Myriadbits/Myriadclock/src/DisplayStateToilet.h

#pragma once

#include "DisplayStateBase.h"

///////////////////////////////////////////////////////////////////////////////
// Base class for all display states
// Command line interpreter
///////////////////////////////////////////////////////////////////////////////
class DisplayStateToilet : public DisplayStateBase
{
public:
    DisplayStateToilet() : DisplayStateBase("toilet") 
    {
    }

    virtual void Initialize(CRGB* pLEDs, BLEConfig* pConfig, DisplayStateManager *pManager);
    virtual bool HandleLoop(unsigned long epochTime, time_t localTime);  

private:
    static uint8_t     s_toiletSign[16 * 16];
    uint8_t     m_nWordIndexTop;
    uint8_t     m_nWordIndexBottom;
};
