Myriadbits/Myriadclock/src/ClockLayoutEN_V2.h

///////////////////////////////////////////////////////////////////////////////
//
// Definition of the myriadclock display layout for the English plate
//
// COPYRIGHT NOTICE                                                           
// ================
// Copyright (c) 2026, Jochem Bakker <Jochem@myriadbits.com>
//
// Published under the Internet Systems Consortium (ISC) license:
// Permission to use, copy, modify, and/or distribute this software for any
// purpose with or without fee is hereby granted, provided that the above
// copyright notice and this permission notice appear in all copies.
//
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
#pragma once

#include "ClockLayoutBase.h"

// How many leds are connected?
#define NUM_LEDS    256
#define NUM_ROWS    16
#define NUM_COLS    16

//
// Latest characters:
//   0123456789012345
// ----------------
// 0|TWENTY-FIVE•TOL•
// 1|TENHALFNPASTOBO•
// 2|QUARTEROPASTORL•
// 3|•BIRTHDAYGOODBT•
// 4|THREEIGHTMORNING
// 5|TWONESEVENOWIFIW
// 6|FOURTWELVEBREAKO
// 7|TENINELEVENFASTR
// 8|FIVESIX•O'CLOCKD
// 9|LUNCHDINNERTIMEC
// 0|MOTUWETHFRSASUNL
// 1|101121314151617O
// 2|181922023242526X
// 3|27282930@JANFEBE
// 4|MARAPRMAYJUNJULL
// 5|AUGSEPOCTNOVDEC•
//


// Word definitions, {-1,-1} or WEND terminated (led numbers start at 0)

static const ledpos_t ENV2_minute_1  [] = { {15,0}, WEND};
static const ledpos_t ENV2_minute_2  [] = { {15,0}, {15,1}, WEND};
static const ledpos_t ENV2_minute_3  [] = { {15,0}, {15,1}, {15,2}, WEND};
static const ledpos_t ENV2_minute_4  [] = { {15,0}, {15,1}, {15,2}, {15,3}, WEND};
static const ledpos_t ENV2_minute_5  [] = { {7,0}, {8,0}, {9,0}, {10,0}, WEND};
static const ledpos_t ENV2_minute_10 [] = { {0,1}, {1,1}, {2,1}, WEND};
static const ledpos_t ENV2_quarter   [] = { {0,2}, {1,2}, {2,2}, {3,2}, {4,2}, {5,2}, {6,2}, WEND};
static const ledpos_t ENV2_minute_20 [] = { {0,0}, {1,0}, {2,0}, {3,0}, {4,0}, {5,0}, WEND};
static const ledpos_t ENV2_minute_25 [] = { {0,0}, {1,0}, {2,0}, {3,0}, {4,0}, {5,0}, {6,0}, {7,0}, {8,0}, {9,0}, {10,0}, WEND};

static const ledpos_t ENV2_pulse     [] = { {15,15}, WEND};

static const ledpos_t ENV2_past1     [] = { {8,1}, {9,1}, {10,1}, {11,1}, WEND};
static const ledpos_t ENV2_past2     [] = { {8,2}, {9,2}, {10,2}, {11,2}, WEND};
static const ledpos_t ENV2_to0       [] = { {12,0}, {13,0}, WEND}; // Line 0
static const ledpos_t ENV2_to1       [] = { {11,1}, {12,1}, WEND}; // Line 1
static const ledpos_t ENV2_to2       [] = { {11,2}, {12,2}, WEND}; // Line 2

static const ledpos_t ENV2_half      [] = { {3,1}, {4,1}, {5,1}, {6,1}, {8,1}, {9,1}, {10,1}, {11,1}, WEND}; // It is always "half past"

static const ledpos_t ENV2_hour_1    [] = { {2,5}, {3,5}, {4,5}, WEND};
static const ledpos_t ENV2_hour_2    [] = { {0,5}, {1,5}, {2,5}, WEND};
static const ledpos_t ENV2_hour_3    [] = { {0,4}, {1,4}, {2,4}, {3,4}, {4,4}, WEND};
static const ledpos_t ENV2_hour_4    [] = { {0,6}, {1,6}, {2,6}, {3,6}, WEND};
static const ledpos_t ENV2_hour_5    [] = { {0,8}, {1,8}, {2,8}, {3,8}, WEND};
static const ledpos_t ENV2_hour_6    [] = { {4,8}, {5,8}, {6,8}, WEND};
static const ledpos_t ENV2_hour_7    [] = { {5,5}, {6,5}, {7,5}, {8,5}, {9,5}, WEND};
static const ledpos_t ENV2_hour_8    [] = { {4,4}, {5,4}, {6,4}, {7,4}, {8,4}, WEND};
static const ledpos_t ENV2_hour_9    [] = { {2,7}, {3,7}, {4,7}, {5,7}, WEND};
static const ledpos_t ENV2_hour_10   [] = { {0,7}, {1,7}, {2,7}, WEND};
static const ledpos_t ENV2_hour_11   [] = { {5,7}, {6,7}, {7,7}, {8,7}, {9,7}, {10,7}, WEND};
static const ledpos_t ENV2_hour_12   [] = { {4,6}, {5,6}, {6,6}, {7,6}, {8,6}, {9,6}, WEND};
static const ledpos_t ENV2_hour_full [] = { {8,8}, {9,8}, {10,8}, {11,8}, {12,8}, {13,8}, {14,8}, WEND};


static const ledpos_t ENV2_monday    [] = { {0,10}, {1,10}, WEND};
static const ledpos_t ENV2_tuesday   [] = { {2,10}, {3,10}, WEND};
static const ledpos_t ENV2_wednesday [] = { {4,10}, {5,10}, WEND};
static const ledpos_t ENV2_thursday  [] = { {6,10}, {7,10}, WEND};
static const ledpos_t ENV2_friday    [] = { {8,10}, {9,10}, WEND};
static const ledpos_t ENV2_saturday  [] = { {10,10}, {11,10}, WEND};
static const ledpos_t ENV2_sunday    [] = { {12,10}, {13,10}, {14,10}, WEND};

static const ledpos_t ENV2_day0      [] = { {1,11}, WEND};
static const ledpos_t ENV2_day1      [] = { {2,11}, WEND};
static const ledpos_t ENV2_day2      [] = { {4,11}, WEND};
static const ledpos_t ENV2_day3      [] = { {6,11}, WEND};
static const ledpos_t ENV2_day4      [] = { {8,11}, WEND};
static const ledpos_t ENV2_day5      [] = { {10,11}, WEND};
static const ledpos_t ENV2_day6      [] = { {12,11}, WEND};
static const ledpos_t ENV2_day7      [] = { {14,11}, WEND};
static const ledpos_t ENV2_day8      [] = { {1,12}, WEND};
static const ledpos_t ENV2_day9      [] = { {3,12}, WEND};
static const ledpos_t ENV2_day10     [] = { {0,11}, {1,11}, WEND};
static const ledpos_t ENV2_day11     [] = { {2,11}, {3,11}, WEND};
static const ledpos_t ENV2_day12     [] = { {3,11}, {4,11}, WEND};
static const ledpos_t ENV2_day13     [] = { {5,11}, {6,11}, WEND};
static const ledpos_t ENV2_day14     [] = { {7,11}, {8,11}, WEND};
static const ledpos_t ENV2_day15     [] = { {9,11}, {10,11}, WEND};
static const ledpos_t ENV2_day16     [] = { {11,11}, {12,11}, WEND};
static const ledpos_t ENV2_day17     [] = { {13,11}, {14,11}, WEND};
static const ledpos_t ENV2_day18     [] = { {0,12}, {1,12}, WEND};
static const ledpos_t ENV2_day19     [] = { {2,12}, {3,12}, WEND};
static const ledpos_t ENV2_day20     [] = { {5,12}, {6,12}, WEND};
static const ledpos_t ENV2_day21     [] = { {4,11}, {5,11}, WEND};
static const ledpos_t ENV2_day22     [] = { {4,12}, {5,12}, WEND};
static const ledpos_t ENV2_day23     [] = { {7,12}, {8,12}, WEND};
static const ledpos_t ENV2_day24     [] = { {9,12}, {10,12}, WEND};
static const ledpos_t ENV2_day25     [] = { {11,12}, {12,12}, WEND};
static const ledpos_t ENV2_day26     [] = { {13,12}, {14,12}, WEND};
static const ledpos_t ENV2_day27     [] = { {0,13}, {1,13}, WEND};
static const ledpos_t ENV2_day28     [] = { {2,13}, {3,13}, WEND};
static const ledpos_t ENV2_day29     [] = { {4,13}, {5,13}, WEND};
static const ledpos_t ENV2_day30     [] = { {6,13}, {7,13}, WEND};
static const ledpos_t ENV2_day31     [] = { {6,11}, {7,11}, WEND};

static const ledpos_t ENV2_januari  [] = { {9,13}, {10,13}, {11,13}, WEND};
static const ledpos_t ENV2_februari [] = { {12,13}, {13,13}, {14,13}, WEND};
static const ledpos_t ENV2_march    [] = { {0,14}, {1,14}, {2,14}, WEND};
static const ledpos_t ENV2_april    [] = { {3,14}, {4,14}, {5,14}, WEND};
static const ledpos_t ENV2_may      [] = { {6,14}, {7,14}, {8,14}, WEND};
static const ledpos_t ENV2_june     [] = { {9,14}, {10,14}, {11,14}, WEND};
static const ledpos_t ENV2_july     [] = { {12,14}, {13,14}, {14,14}, WEND};
static const ledpos_t ENV2_august   [] = { {0,15}, {1,15}, {2,15}, WEND};
static const ledpos_t ENV2_september[] = { {3,15}, {4,15}, {5,15}, WEND};
static const ledpos_t ENV2_october  [] = { {6,15}, {7,15}, {8,15}, WEND};
static const ledpos_t ENV2_november [] = { {9,15}, {10,15}, {11,15}, WEND};
static const ledpos_t ENV2_december [] = { {12,15}, {13,15}, {14,15}, WEND};

static const ledpos_t ENV2_cloxel  [] = { {15,9}, {15,10}, {15,11}, {15,12}, {15,13}, {15,14}, WEND};
static const ledpos_t ENV2_word  [] = { {15,5}, {15,6}, {15,7}, {15,8}, WEND};
static const ledpos_t ENV2_bt [] = { {13,3}, {14,3}, WEND};
static const ledpos_t ENV2_passcode [] = { WEND};
static const ledpos_t ENV2_no  [] = { {9,5}, {10,5}, WEND};
static const ledpos_t ENV2_yes  [] = { {9,3}, {10,3}, {11,3}, {12,3}, WEND}; // Actually = GOOD
static const ledpos_t ENV2_wifi  [] = { {11,5}, {12,5}, {13,5}, {14,5}, WEND};

static const ledpos_t ENV2_birthday [] = { {1,3}, {2,3}, {3,3}, {4,3}, {5,3}, {6,3}, {7,3}, {8,3}, WEND};
static const ledpos_t ENV2_holiday [] = { WEND};
static const ledpos_t ENV2_party [] = { {6,3}, {7,3}, {8,3}, WEND}; // Actually not available, will display 'day'
static const ledpos_t ENV2_wakeup [] = { WEND};
static const ledpos_t ENV2_goodmorning [] = { {9,3}, {10,3}, {11,3}, {12,3}, {9,4}, {10,4}, {11,4}, {12,4}, {13,4}, {14,4}, {15,4}, WEND};

static const ledpos_t ENV2_breakfast [] = { {10,6}, {11,6}, {12,6}, {13,6}, {14,6}, {11,7}, {12,7}, {13,7}, {14,7}, WEND};
static const ledpos_t ENV2_lunch [] = { {0,9}, {1,9}, {2,9}, {3,9}, {4,9}, {11,9}, {12,9}, {13,9}, {14,9}, WEND};
static const ledpos_t ENV2_dinner [] = { {5,9}, {6,9}, {7,9}, {8,9}, {9,9}, {10,9}, {11,9}, {12,9}, {13,9}, {14,9}, WEND};

//
// EN clock layout V1
//
static const ledclocklayout_t s_layoutEN_V2 = 
{
    16,
    16,
    256,
    O_NORMAL,
    false,

    // Time display method
    TF_EN_5MIN,

    // Time parts
    {
        ENV2_pulse, EMPTY, ENV2_minute_1, ENV2_minute_2, ENV2_minute_3, ENV2_minute_4, ENV2_minute_5, EMPTY, EMPTY, EMPTY, EMPTY, ENV2_minute_10,
        EMPTY, EMPTY, EMPTY, EMPTY, ENV2_quarter, ENV2_minute_20, ENV2_minute_25, 
        ENV2_past2, ENV2_to0, ENV2_past1, ENV2_to1, ENV2_past2, ENV2_to2, ENV2_past1, ENV2_to0, ENV2_past2, ENV2_to0, 
        ENV2_half, ENV2_half, ENV2_hour_full
    },

    // 12x Hours
    {
        ENV2_hour_12, ENV2_hour_1, ENV2_hour_2, ENV2_hour_3, ENV2_hour_4, ENV2_hour_5, ENV2_hour_6, ENV2_hour_7, ENV2_hour_8, ENV2_hour_9, ENV2_hour_10, ENV2_hour_11         
    },

    // 7x Day of the week
    {
        ENV2_sunday, ENV2_monday, ENV2_tuesday, ENV2_wednesday, ENV2_thursday, ENV2_friday, ENV2_saturday
    },

    // 31x Day number
    {
        ENV2_day1, ENV2_day2, ENV2_day3, ENV2_day4, ENV2_day5, ENV2_day6, ENV2_day7, ENV2_day8, ENV2_day9, ENV2_day10, 
        ENV2_day11, ENV2_day12, ENV2_day13, ENV2_day14, ENV2_day15, ENV2_day16, ENV2_day17, ENV2_day18, ENV2_day19, ENV2_day20, 
        ENV2_day21, ENV2_day22, ENV2_day23, ENV2_day24, ENV2_day25, ENV2_day26, ENV2_day27, ENV2_day28, ENV2_day29, ENV2_day30, 
        ENV2_day31
    },

    // 12x Month
    {
        ENV2_januari, ENV2_februari, ENV2_march, ENV2_april, ENV2_may, ENV2_june, ENV2_july, ENV2_august, ENV2_september, ENV2_october, ENV2_november, ENV2_december
    },

    // Extra parts
    {
        ENV2_no,
        ENV2_yes,
        ENV2_wifi,
        ENV2_cloxel,
        ENV2_word,
        EMPTY,
        ENV2_bt,
        ENV2_passcode,
        ENV2_goodmorning,
        ENV2_birthday,
        ENV2_holiday,
        ENV2_party,
        ENV2_wakeup,
        ENV2_breakfast,
        ENV2_lunch,
        ENV2_dinner,
    },

    // 10x number
    {
        ENV2_day0, ENV2_day1, ENV2_day2, ENV2_day3, ENV2_day4, ENV2_day5, ENV2_day6, ENV2_day7, ENV2_day8, ENV2_day9
    }
};
