Myriadbits/Myriadclock/src/Myriadbitsfont5x6_3.h

#include "FontsBase.h"

const uint8_t JochemFont56Bitmaps[] PROGMEM = {
	0x55, 0x00, 0xB4, 0x00, 0x00, 0x00, 0x5F, 0x00, 
	0x06, 0xF8, 0x00, 0x00, 0x92, 0x00, 0x0A, 0xA0, 
	0x00, 0xC0, 0x6A, 0x00, 0x95, 0x00, 0x02, 0xA0, 
	0x00, 0x05, 0x00, 0x00, 0x12, 0x00, 0xF6, 0xDE, 
	0x00, 0xF8, 0xE7, 0xCE, 0x00, 0xE7, 0x9E, 0x00, 
	0xB7, 0x92, 0x00, 0xF3, 0x9E, 0x00, 0xF3, 0xDE, 
	0x00, 0xE4, 0x92, 0x00, 0xF7, 0xDE, 0x00, 0xF7, 
	0x9E, 0x00, 0x50, 0x58, 0x2A, 0x22, 0x00, 0x03, 
	0x80, 0x00, 0x88, 0xA8, 0x00, 0xE5, 0x04, 0x00, 
	0x6B, 0xB8, 0x70, 0xF7, 0xDA, 0x00, 0xD7, 0x5C, 
	0x00, 0xF2, 0x4E, 0x00, 0xD6, 0xDC, 0x00, 0xF3, 
	0x4E, 0x00, 0xF3, 0x48, 0x00, 0xF2, 0xDE, 0x00, 
	0xB7, 0xDA, 0x00, 0xF8, 0x24, 0xDE, 0x00, 0xAA, 
	0xCA, 0x90, 0x92, 0x4E, 0x00, 0xFD, 0x6B, 0x5A, 
	0x80, 0xF9, 0x99, 0x90, 0xF6, 0xDE, 0x00, 0xF7, 
	0xC8, 0x00, 0xF7, 0x92, 0x00, 0xF7, 0x5A, 0x00, 
	0x71, 0x1C, 0x00, 0xE9, 0x24, 0x00, 0xB6, 0xDE, 
	0x00, 0xB6, 0xD4, 0x00, 0x8D, 0x6B, 0x5F, 0x80, 
	0xB5, 0x5A, 0x00, 0xB5, 0x24, 0x00, 0xE5, 0x4E, 
	0x00, 0xEA, 0xC0, 0x08, 0x42, 0x10, 0xD5, 0xC0, 
	0x54, 0x00, 0x00, 0x00, 0x00, 0x0F, 0xC0, 0x1E, 
	0xFA, 0x00, 0x13, 0xDE, 0x00, 0x1E, 0x4E, 0x00, 
	0x07, 0xDE, 0x00, 0x1F, 0xCE, 0x00, 0x1E, 0x68, 
	0x00, 0x1E, 0x5E, 0x00, 0x13, 0xDA, 0x00, 0x78, 
	0x15, 0xC0, 0x17, 0x6A, 0x00, 0x2A, 0xC0, 0x07, 
	0xEB, 0x5A, 0x80, 0x1E, 0xDA, 0x00, 0x1E, 0xDE, 
	0x00, 0x1E, 0xF8, 0x00, 0x1E, 0xF2, 0x00, 0x1E, 
	0x48, 0x00, 0x1F, 0x3E, 0x00, 0x1D, 0x24, 0x00, 
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
	{ 84, 3, 6, 4, 0, -5 },  // 0x44 'D'
	{ 87, 3, 6, 4, 0, -5 },  // 0x45 'E'
	{ 90, 3, 6, 4, 0, -5 },  // 0x46 'F'
	{ 93, 3, 6, 4, 0, -5 },  // 0x47 'G'
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

const GFXfont JochemFont56 PROGMEM = {
	(uint8_t*)JochemFont56Bitmaps,
	(GFXglyph*)JochemFont56Glyphs,
	0x20, 0x7E, 6 };
