Myriadbits/Myriadclock/src/Myriadbitsfont5x8_3.h

#include "FontsBase.h"

const uint8_t JochemFont58Bitmaps[] PROGMEM = {
	0xFA, 0xB4, 0x00, 0x00, 0x00, 0x5F, 0x55, 0xF5, 
	0x06, 0xF8, 0xF1, 0xF6, 0x00, 0x92, 0x49, 0x00, 
	0x04, 0xA4, 0xBA, 0x50, 0xC0, 0x6A, 0xA4, 0x95, 
	0x58, 0x02, 0xAE, 0xA8, 0x01, 0x2E, 0x90, 0x00, 
	0x06, 0x00, 0x00, 0xF0, 0x00, 0x02, 0x00, 0x12, 
	0x48, 0x00, 0x69, 0x99, 0x99, 0x60, 0xD5, 0x54, 
	0x69, 0x12, 0x48, 0xF0, 0x69, 0x21, 0x19, 0x60, 
	0x35, 0x9F, 0x11, 0x10, 0xF8, 0xE1, 0x19, 0x60, 
	0x78, 0xE9, 0x99, 0x60, 0xF1, 0x24, 0x88, 0x80, 
	0x69, 0x69, 0x99, 0x60, 0x69, 0x99, 0x71, 0xE0, 
	0x24, 0x04, 0x16, 0x12, 0x48, 0x42, 0x10, 0x00, 
	0x71, 0xC0, 0x84, 0x21, 0x24, 0x80, 0x54, 0xA4, 
	0x10, 0x69, 0xBB, 0xB8, 0x60, 0x69, 0xF9, 0x99, 
	0x90, 0xE9, 0xE9, 0x99, 0xE0, 0x69, 0x88, 0x89, 
	0x60, 0xCA, 0x99, 0x9A, 0xC0, 0xF8, 0xE8, 0x88, 
	0xF0, 0xF8, 0xE8, 0x88, 0x80, 0x69, 0x88, 0xB9, 
	0x60, 0x99, 0xF9, 0x99, 0x90, 0xE9, 0x24, 0xB8, 
	0x11, 0x11, 0x99, 0x60, 0x9A, 0xCA, 0x99, 0x90, 
	0x88, 0x88, 0x88, 0xF0, 0x9F, 0xF9, 0x99, 0x90, 
	0x99, 0xDB, 0x99, 0x90, 0x69, 0x99, 0x99, 0x60, 
	0xE9, 0xE8, 0x88, 0x80, 0x69, 0x9B, 0xDB, 0x60, 
	0xE9, 0xEC, 0xA9, 0x90, 0x68, 0x61, 0x19, 0x60, 
	0xE9, 0x24, 0x90, 0x99, 0x99, 0x99, 0x60, 0x99, 
	0x99, 0x66, 0x60, 0x8C, 0x63, 0x5A, 0xD5, 0x40, 
	0x99, 0x66, 0x69, 0x90, 0xB6, 0xD4, 0x90, 0xF1, 
	0x24, 0x88, 0xF0, 0xF2, 0x49, 0x38, 0x00, 0x84, 
	0x21, 0x00, 0xE4, 0x92, 0x78, 0x0A, 0x80, 0x00, 
	0x00, 0x00, 0x00, 0x0F, 0xC0, 0x00, 0x61, 0x79, 
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
	{ 113, 4, 8, 5, 0, -7 },  // 0x44 'D'
	{ 117, 4, 8, 5, 0, -7 },  // 0x45 'E'
	{ 121, 4, 8, 5, 0, -7 },  // 0x46 'F'
	{ 125, 4, 8, 5, 0, -7 },  // 0x47 'G'
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

const GFXfont JochemFont58 PROGMEM = {
	(uint8_t*)JochemFont58Bitmaps,
	(GFXglyph*)JochemFont58Glyphs,
	0x20, 0x7E, 8 };
