Myriadbits/Myriadclock/src/MyriadclockConfig.h

#pragma once

#define FIRMWARE_VERSION      4       // Myriadclock firmware version
#define FOTA_NAME             "Myriadclock-fota"
#define FOTA_VERSION          4
#define FOTA_URL              "http://myriadclock.myriadbits.com/myriadclock-fota.json"
