Myriadbits/Myriadclock/src/HighFont4x6.h

#include "FontsBase.h"

const uint8_t Highfont4x6Bitmaps[] PROGMEM = {
		0xF4, 0xB4, 0x00, 0x00, 0x05, 0xF5, 0x5F, 0x00, 
	0x05, 0x40, 0x18, 0x05, 0x29, 0x00, 0x11, 0x22, 
	0x40, 0x01, 0x74, 0x00, 0x25, 0x29, 0x00, 0xF6, 
	0xDB, 0xC0, 0xFC, 0xE7, 0xC9, 0xC0, 0xE7, 0x93, 
	0xC0, 0xB7, 0x92, 0x40, 0xF3, 0x93, 0xC0, 0xF3, 
	0xDB, 0xC0, 0xE4, 0x92, 0x40, 0xF7, 0xDB, 0xC0, 
	0xF7, 0x92, 0x40, 0x3C, 0xF0, 0x2C, 0x2A, 0x44, 
	0x40, 0x0C, 0xC0, 0x88, 0x95, 0x00, 0xF4, 0xA0, 
	0x80, 0xF7, 0xDB, 0xC0, 0xF7, 0xDB, 0x40, 0xF7, 
	0x5B, 0xC0, 0xF6, 0x4B, 0xC0, 0xD6, 0xDB, 0x80, 
	0xF3, 0xC9, 0xC0, 0xF3, 0xC9, 0x00, 0xF2, 0x5B, 
	0xC0, 0xB7, 0xDB, 0x40, 0xFC, 0x24, 0x93, 0xC0, 
	0xB7, 0x5B, 0x40, 0x92, 0x49, 0xC0, 0xBF, 0xDB, 
	0x40, 0xF6, 0xDB, 0x40, 0xF6, 0xDB, 0xC0, 0xF7, 
	0xC9, 0x00, 0xF6, 0xDF, 0xC0, 0xF6, 0xEB, 0x40, 
	0xF3, 0x93, 0xC0, 0xE9, 0x24, 0x80, 0xB6, 0xDB, 
	0xC0, 0xB6, 0xDA, 0x80, 0xB6, 0xFF, 0x40, 0xB5, 
	0x5B, 0x40, 0xB5, 0x24, 0x80, 0xE5, 0x49, 0xC0, 
	0xEA, 0xB0, 0x91, 0x22, 0x40, 0xD5, 0x70, 0x0A, 
	0x80, 0x00, 0x00, 0x01, 0xC0, 0x90, 0x00, 0x1C, 
	0xFB, 0xC0, 0x13, 0xDB, 0xC0, 0x1E, 0x49, 0xC0, 
	0x07, 0xDB, 0xC0, 0x1E, 0xF9, 0xC0, 0x1E, 0x69, 
	0x00, 0x1E, 0xF3, 0xC0, 0x13, 0xDB, 0x40, 0x5C, 
	0x11, 0x70, 0x12, 0xED, 0x40, 0x7C, 0x17, 0xFB, 
	0x40, 0x1E, 0xDB, 0x40, 0x1E, 0xDB, 0xC0, 0x1E, 
	0xF9, 0x00, 0x1E, 0xF2, 0x40, 0x1E, 0xC9, 0x00, 
	0x0E, 0x73, 0x80, 0x2E, 0xB0, 0x16, 0xDB, 0xC0, 
	0x16, 0xD4, 0x80, 0x16, 0xFF, 0x40, 0x16, 0xAB, 
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
	{ 77, 3, 6, 4, 0, -4 },  // 0x44 'D'
	{ 80, 3, 6, 4, 0, -4 },  // 0x45 'E'
	{ 83, 3, 6, 4, 0, -4 },  // 0x46 'F'
	{ 86, 3, 6, 4, 0, -4 },  // 0x47 'G'
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

const GFXfont Highfont4x6 PROGMEM = {
	(uint8_t*)Highfont4x6Bitmaps,
	(GFXglyph*)Highfont4x6Glyphs,
	0x20, 0x7E, 6 };
