Myriadbits/Myriadclock/src/HighFont4x8.h

#include "FontsBase.h"

const uint8_t Highfont4x8Bitmaps[] PROGMEM = {
	0xFD, 0xB4, 0x00, 0x00, 0x05, 0xF5, 0x5F, 0x50, 
	0x00, 0x05, 0x55, 0x18, 0x05, 0x29, 0x24, 0x11, 
	0x22, 0x49, 0x01, 0x74, 0x00, 0x00, 0x00, 0x17, 
	0x00, 0x00, 0x07, 0x05, 0x5A, 0xF6, 0xDB, 0x6F, 
	0xFF, 0xE7, 0xC9, 0x27, 0xE7, 0x92, 0x4F, 0xB7, 
	0x92, 0x49, 0xF3, 0x92, 0x4F, 0xF3, 0xDB, 0x6F, 
	0xE4, 0x92, 0x49, 0xF7, 0xDB, 0x6F, 0xF7, 0x92, 
	0x49, 0x28, 0x2C, 0x2A, 0x48, 0x88, 0x03, 0x8E, 
	0x00, 0x88, 0x95, 0x00, 0xF4, 0xB4, 0x82, 0xF7, 
	0xDB, 0x6F, 0xF7, 0xDB, 0x6D, 0xF6, 0xEB, 0x6F, 
	0xF6, 0x49, 0x2F, 0xD6, 0xDB, 0x6E, 0xF3, 0xC9, 
	0x27, 0xF3, 0xC9, 0x24, 0xF2, 0x5B, 0x6F, 0xB7, 
	0xDB, 0x6D, 0xFF, 0x24, 0x92, 0x6F, 0xB7, 0x5B, 
	0x6D, 0x92, 0x49, 0x27, 0xBF, 0xDB, 0x6D, 0xF6, 
	0xDB, 0x6D, 0xF6, 0xDB, 0x6F, 0xF7, 0xC9, 0x24, 
	0xF6, 0xDB, 0xEF, 0xF6, 0xEB, 0x6D, 0xF3, 0x92, 
	0x6F, 0xE9, 0x24, 0x92, 0xB6, 0xDB, 0x6F, 0xB6, 
	0xDB, 0x6A, 0xB6, 0xDB, 0xFD, 0xB5, 0x5B, 0x6D, 
	0xB5, 0x24, 0x92, 0xE5, 0x49, 0x27, 0xF2, 0x49, 
	0x27, 0xAA, 0x55, 0xE4, 0x92, 0x4F, 0x01, 0x50, 
	0x00, 0x00, 0x00, 0x07, 0x90, 0x00, 0x00, 0x73, 
	0xEF, 0x92, 0x49, 0xAE, 0x00, 0x01, 0xE7, 0x24, 
	0x92, 0xEB, 0x00, 0x7B, 0xE7, 0x00, 0x79, 0xE4, 
	0x00, 0x3A, 0xCF, 0x92, 0x49, 0xAD, 0x17, 0x01, 
	0x17, 0x92, 0x49, 0x75, 0xFF, 0x00, 0x0B, 0xED, 
	0x00, 0x05, 0x6D, 0x00, 0x05, 0x6A, 0x00, 0x6B, 
	0xA4, 0x00, 0x3A, 0xC9, 0x00, 0x7B, 0x24, 0x00, 
	0x78, 0x8F, 0xAA, 0xBA, 0x00, 0x0B, 0x6F, 0x00, 
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
	{ 83, 3, 8, 4, 0, -6 },  // 0x44 'D'
	{ 86, 3, 8, 4, 0, -6 },  // 0x45 'E'
	{ 89, 3, 8, 4, 0, -6 },  // 0x46 'F'
	{ 92, 3, 8, 4, 0, -6 },  // 0x47 'G'
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

const GFXfont Highfont4x8 PROGMEM = {
	(uint8_t*)Highfont4x8Bitmaps,
	(GFXglyph*)Highfont4x8Glyphs,
	0x20, 0x7E, 8 };
